Bunnykillcz/OpenAlarm/docs/img/OA-mounting.jpg

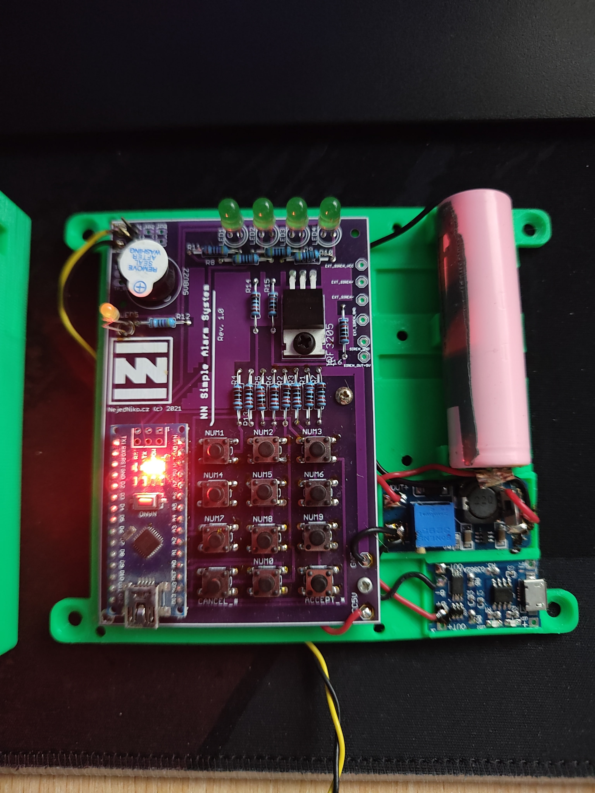
docs/img/OA-mounting.jpg
