Bunnykillcz/OpenAlarm/docs/img/OA-mounting_detail.jpg

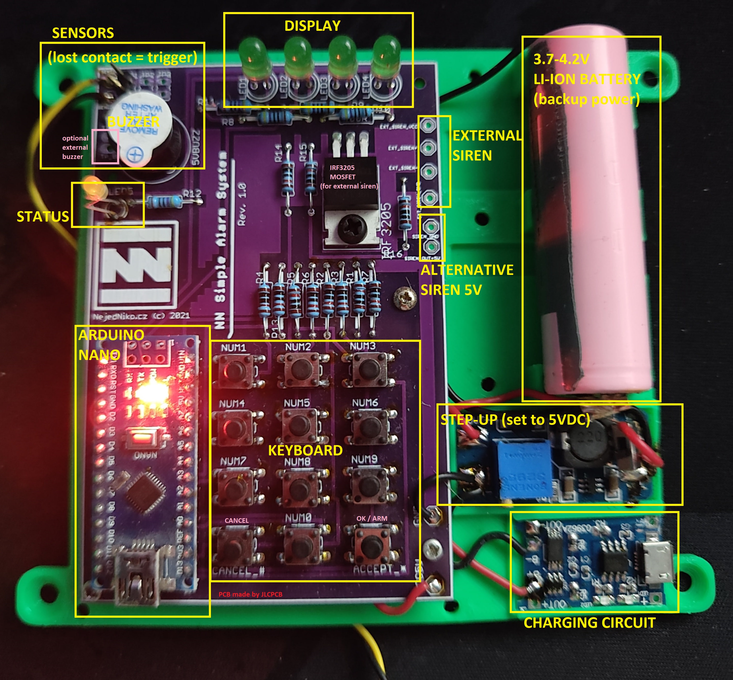
docs/img/OA-mounting_detail.jpg
